lbs2017vuchihung-ops/Robot-aim-system-IOT/hardware/Main Aim to use/Main aim 3MG996R + 1SG90/Arduino based Robot Arm - 7322664/images/gear1.png

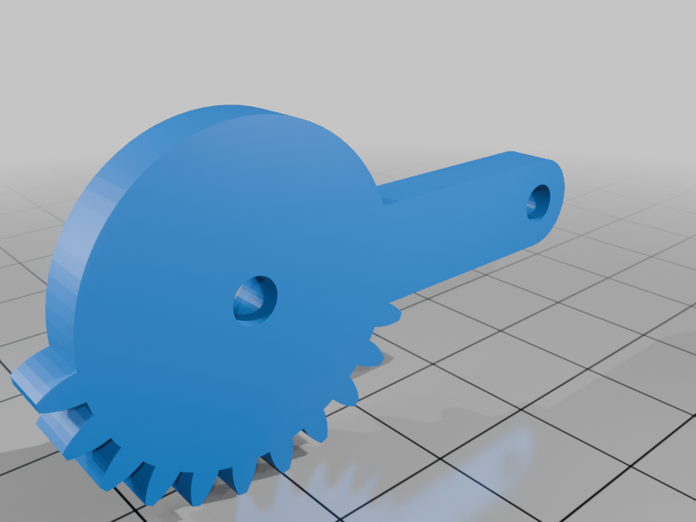
hardware/Main Aim to use/Main aim 3MG996R + 1SG90/Arduino based Robot Arm - 7322664/images/gear1.png
