lbs2017vuchihung-ops/Robot-aim-system-IOT/hardware/Reference Aims/EEZYbotARM MK2 - 1454048 - part 1 of 2/images/b436ef58e6b25d29e519d9658bfed57a.png

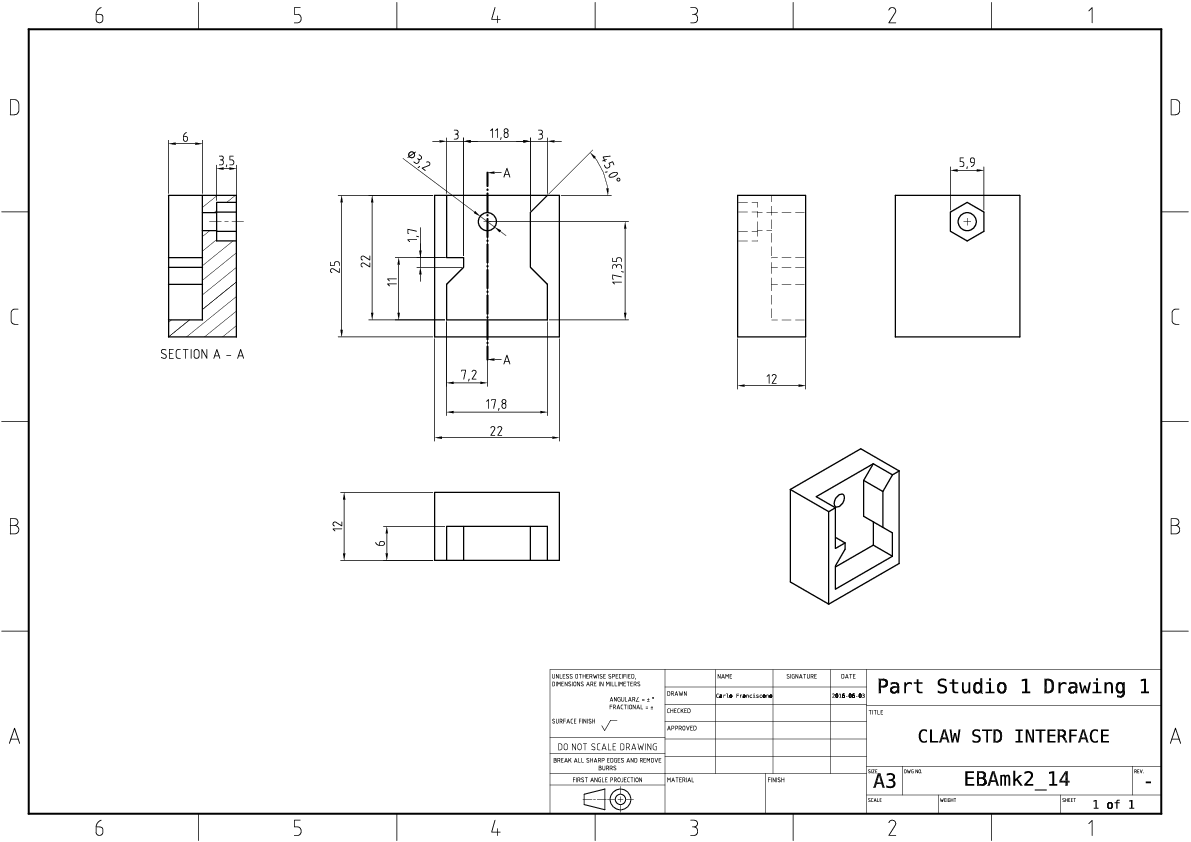
hardware/Reference Aims/EEZYbotARM MK2 - 1454048 - part 1 of 2/images/b436ef58e6b25d29e519d9658bfed57a.png
