lbs2017vuchihung-ops/Robot-aim-system-IOT/hardware/Reference Aims/Micro Servo SG90 - Dummy - 2933842/images/Micro_Servo_SG90.png

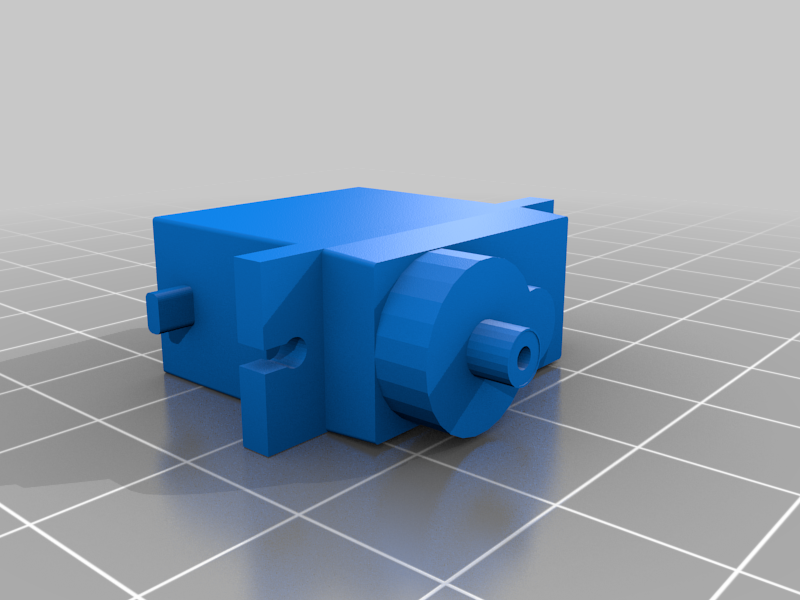
hardware/Reference Aims/Micro Servo SG90 - Dummy - 2933842/images/Micro_Servo_SG90.png
