lbs2017vuchihung-ops/Robot-aim-system-IOT/hardware/Reference Aims/Robotic arm 3 DOF V1 - 6986935/images/Starting_position_for_the_provided_code.jpg

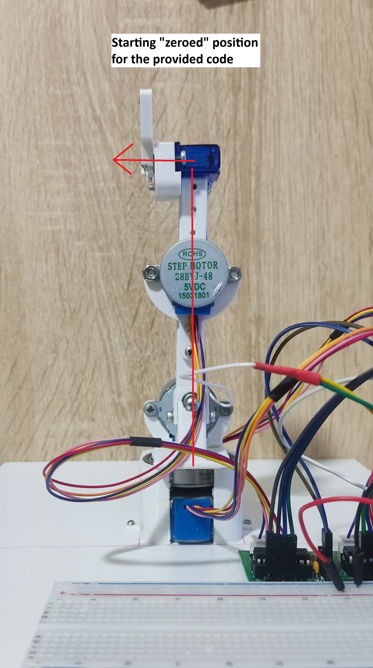
hardware/Reference Aims/Robotic arm 3 DOF V1 - 6986935/images/Starting_position_for_the_provided_code.jpg
