lbs2017vuchihung-ops/Robot-aim-system-IOT/hardware/Reference Aims/Robotic arm 3 DOF V1 - 6986935/images/View_1.jpg

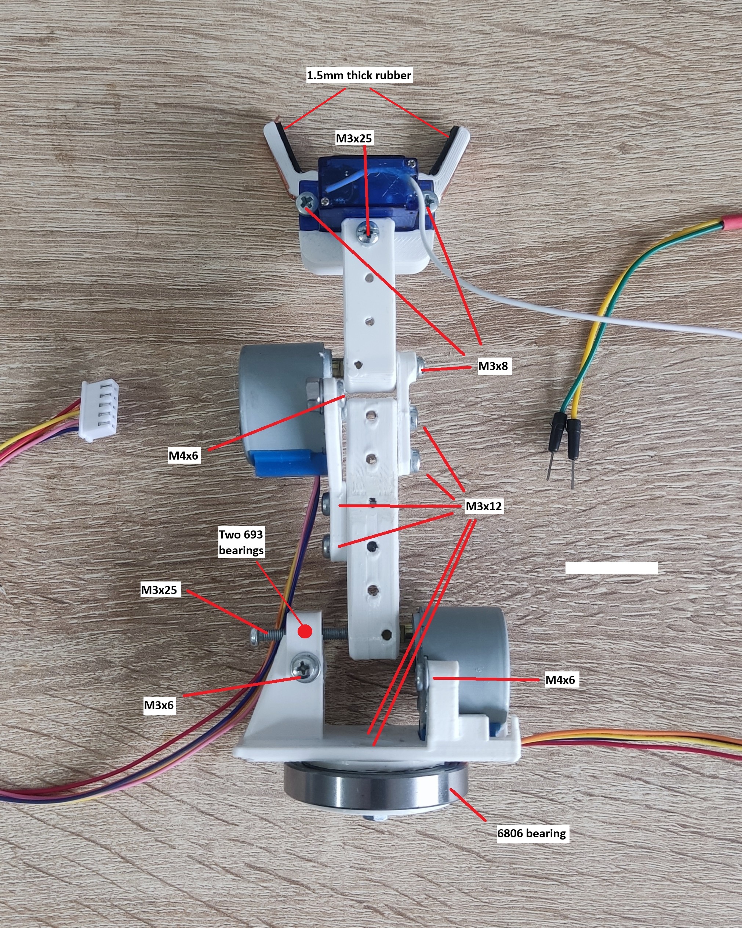
hardware/Reference Aims/Robotic arm 3 DOF V1 - 6986935/images/View_1.jpg
