lbs2017vuchihung-ops/Robot-aim-system-IOT/hardware/Reference Aims/Robotic Arm - 4 DOF - 3888877/images/photo5805476898975887829.jpg

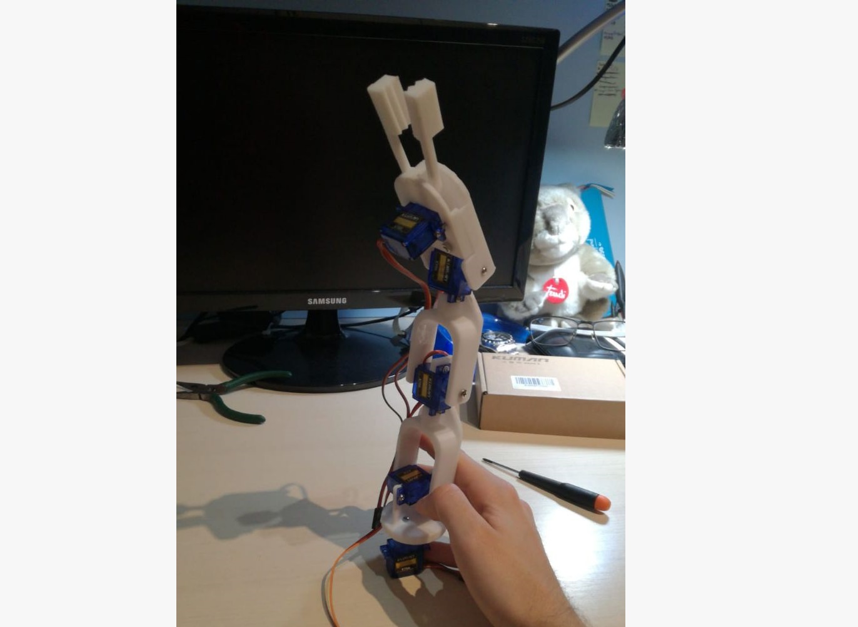
hardware/Reference Aims/Robotic Arm - 4 DOF - 3888877/images/photo5805476898975887829.jpg
