lbs2017vuchihung-ops/Robot-aim-system-IOT/hardware/Reference Aims/Robotic Arm - 4 DOF - 3888877/images/prt0003.png

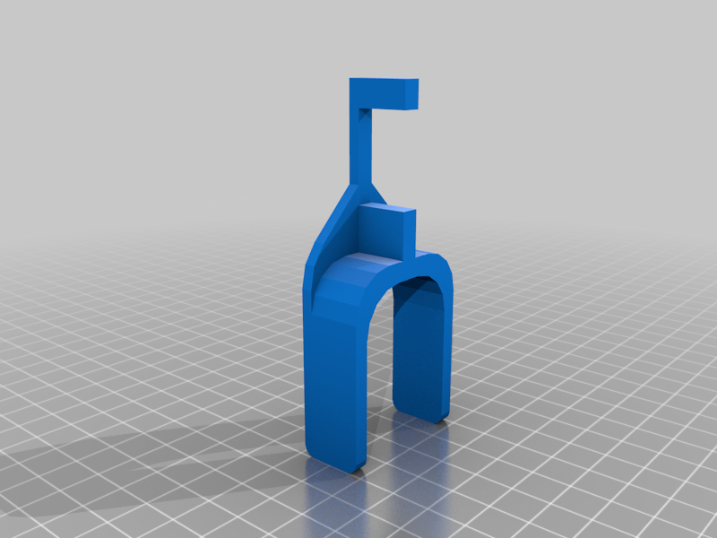
hardware/Reference Aims/Robotic Arm - 4 DOF - 3888877/images/prt0003.png
