lbs2017vuchihung-ops/Robot-aim-system-IOT/hardware/Reference Aims/Servo Arm_Horn for Tower Pro MG995_MG996R - 4719421/images/Servo_Arm.png

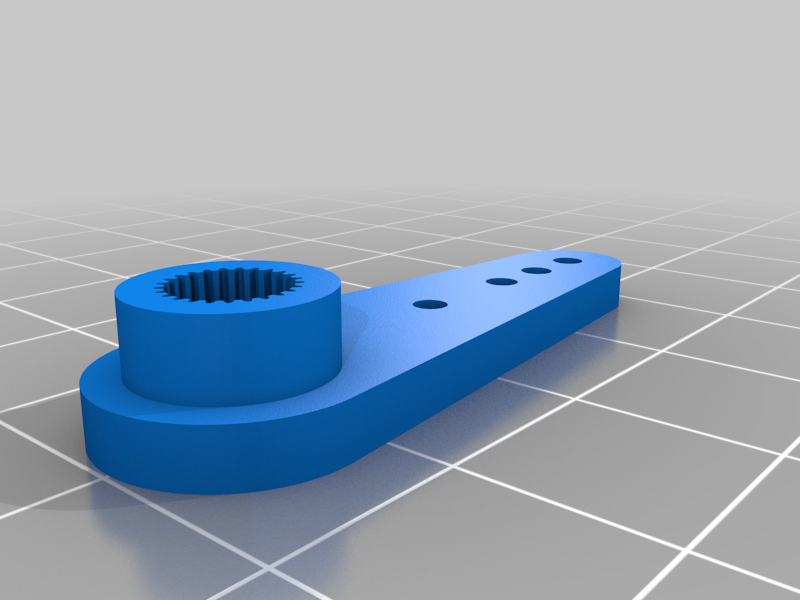
hardware/Reference Aims/Servo Arm_Horn for Tower Pro MG995_MG996R - 4719421/images/Servo_Arm.png
