lbs2017vuchihung-ops/Robot-aim-system-IOT/hardware/Reference Aims/Versatile Servo Bracket System - 5784/images/Servo_BracketOutsideLongV1.1.jpg

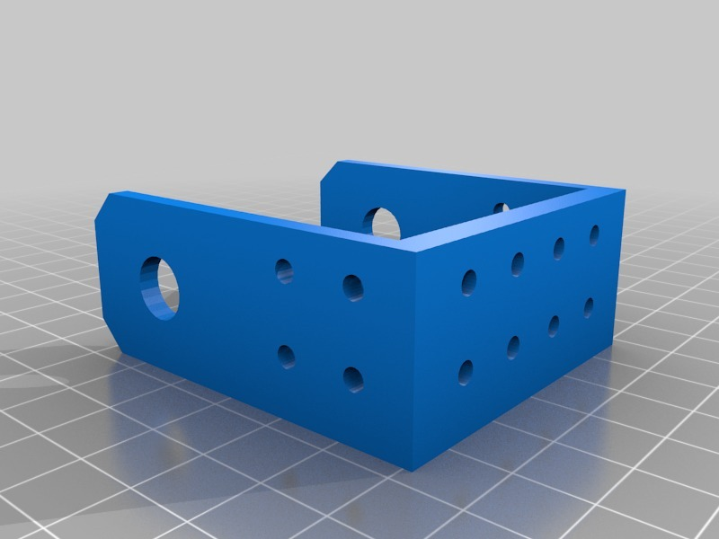
hardware/Reference Aims/Versatile Servo Bracket System - 5784/images/Servo_BracketOutsideLongV1.1.jpg
