lbs2017vuchihung-ops/Robot-aim-system-IOT/hardware/Reference Aims/Versatile Servo Bracket System - 5784/images/Servo_button.jpg

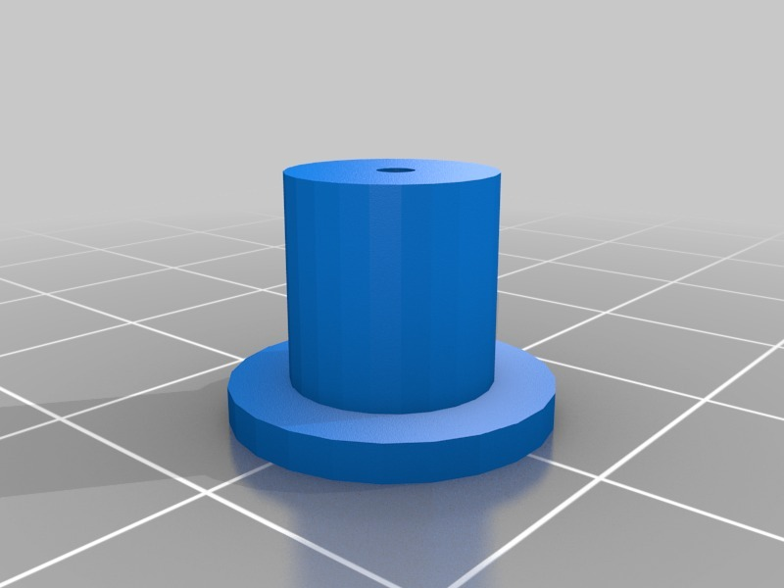
hardware/Reference Aims/Versatile Servo Bracket System - 5784/images/Servo_button.jpg
