lbs2017vuchihung-ops/Robot-aim-system-IOT/hardware/Reference Aims/Versatile Servo Bracket System - 5784/images/Servo_with_Button_display_large.jpg

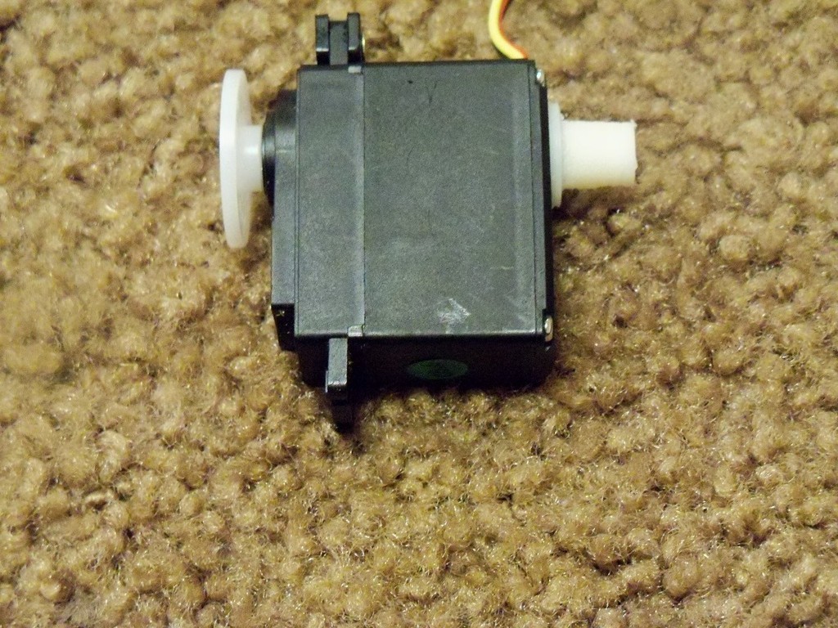
hardware/Reference Aims/Versatile Servo Bracket System - 5784/images/Servo_with_Button_display_large.jpg
