lbs2017vuchihung-ops/Robot-aim-system-IOT/web_app/assets/anh_adruino.png

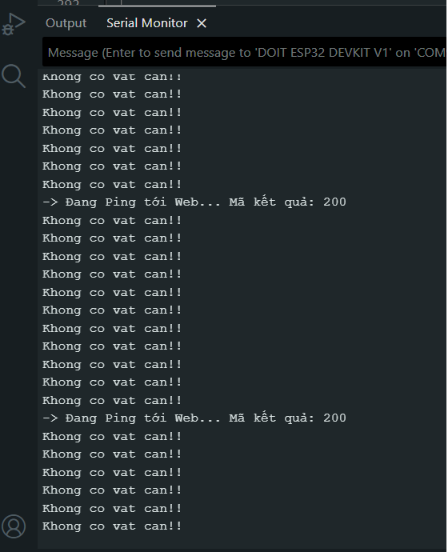
web_app/assets/anh_adruino.png
