lbs2017vuchihung-ops/Robot-aim-system-IOT/web_app/assets/anh_web.png

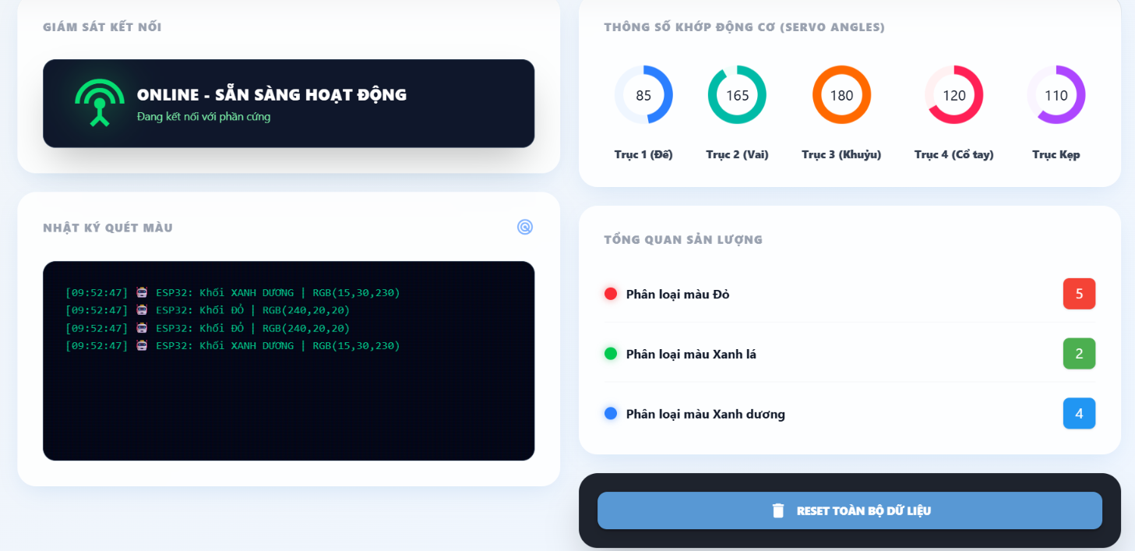
web_app/assets/anh_web.png
