lbs2017vuchihung-ops/Robot-aim-system-IOT/web_app/assets/RobotAimImg.jpg

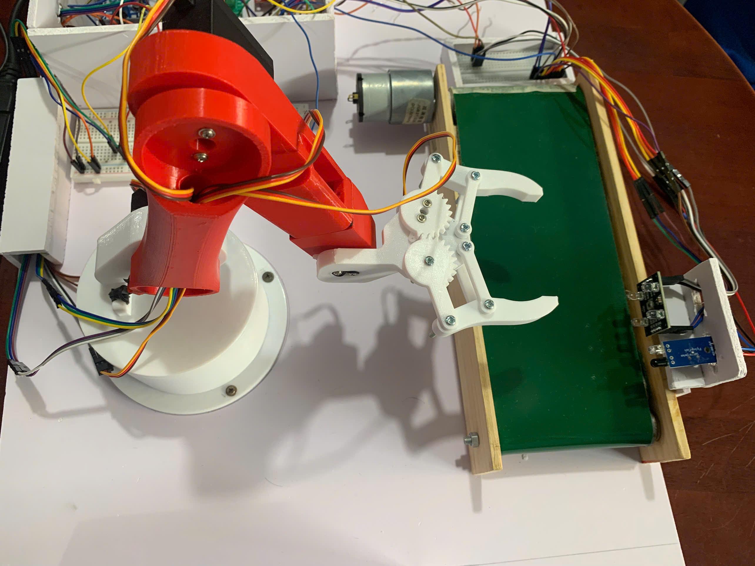
web_app/assets/RobotAimImg.jpg
