lbs2017vuchihung-ops/Robot-aim-system-IOT/hardware/Reference Aims/Versatile Servo Bracket System - 5784/images/Printed_Parts_display_large.jpg

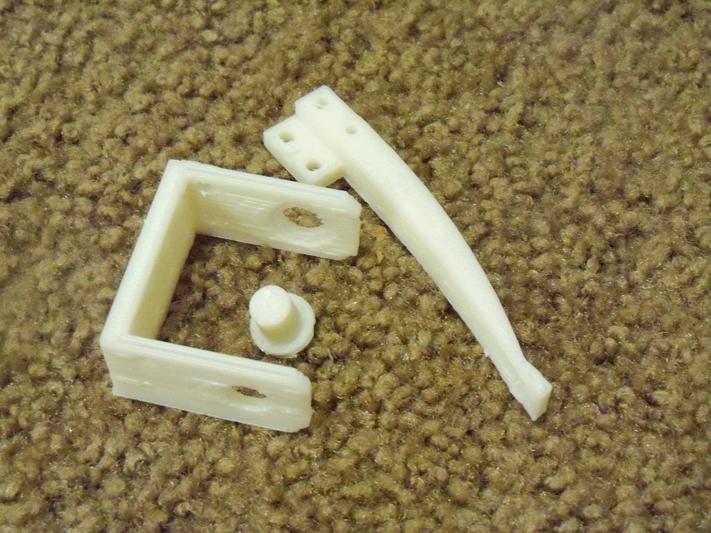
hardware/Reference Aims/Versatile Servo Bracket System - 5784/images/Printed_Parts_display_large.jpg
