lbs2017vuchihung-ops/Robot-aim-system-IOT/hardware/Reference Aims/Robotic Arm - 4 DOF - 3888877/files/prt0003.stl

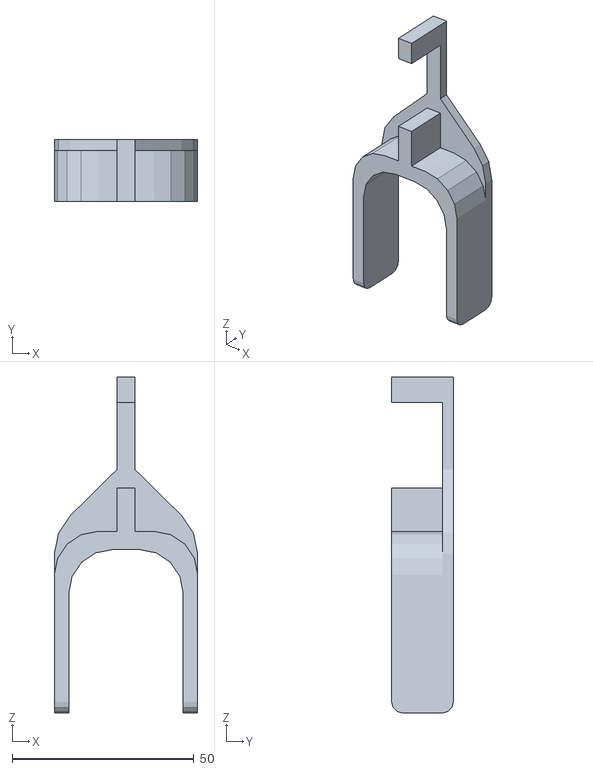
[picture p143: CAD file, 2026-08-05]
hardware/Reference Aims/Robotic Arm - 4 DOF - 3888877/files/prt0003.stl
39.5 x 17.0 x 92.5
