lbs2017vuchihung-ops/Robot-aim-system-IOT/hardware/Reference Aims/Robotic arm 3 DOF V1 - 6986935/files/28byj_mount.stl

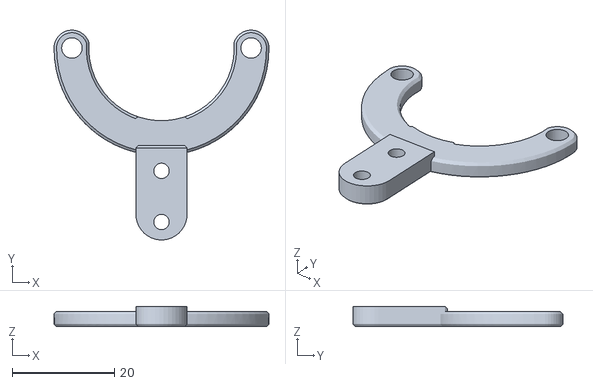
[picture p144: CAD file, 2026-08-05]
hardware/Reference Aims/Robotic arm 3 DOF V1 - 6986935/files/28byj_mount.stl
42.0 x 41.0 x 4.00
