lbs2017vuchihung-ops/Robot-aim-system-IOT/hardware/Reference Aims/Versatile Servo Bracket System - 5784/files/Servo_BracketInsideShortV1.1.stl

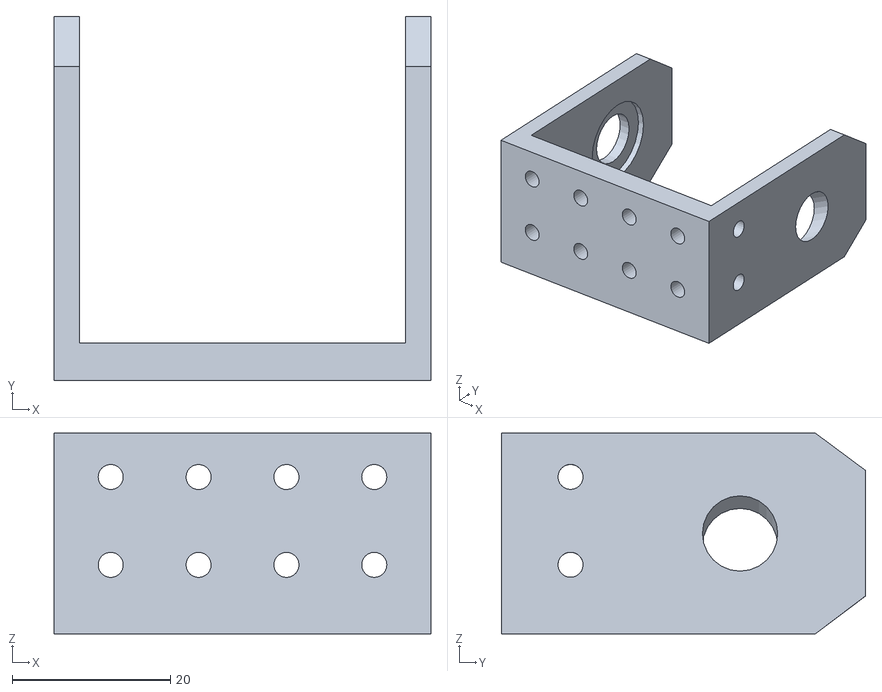
[picture p145: CAD file, 2026-08-05]
hardware/Reference Aims/Versatile Servo Bracket System - 5784/files/Servo_BracketInsideShortV1.1.stl
47.6 x 46.0 x 25.4
