lbs2017vuchihung-ops/Robot-aim-system-IOT/hardware/Main Aim to use/Main aim 3MG996R + 1SG90/Arduino based Robot Arm - 7322664/files/Arm_02_v3.STL

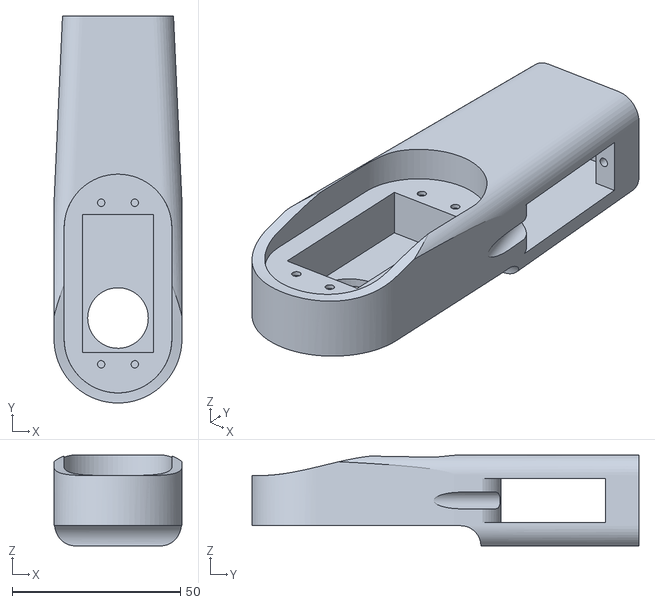
[picture p146: CAD file, 2026-08-05]
hardware/Main Aim to use/Main aim 3MG996R + 1SG90/Arduino based Robot Arm - 7322664/files/Arm_02_v3.STL
38.0 x 115.0 x 27.0
