lbs2017vuchihung-ops/Robot-aim-system-IOT/hardware/Reference Aims/EEZYbotARM MK2 - 1454048 - part 2 of 2/files/EBAmk2_003_varm.STL

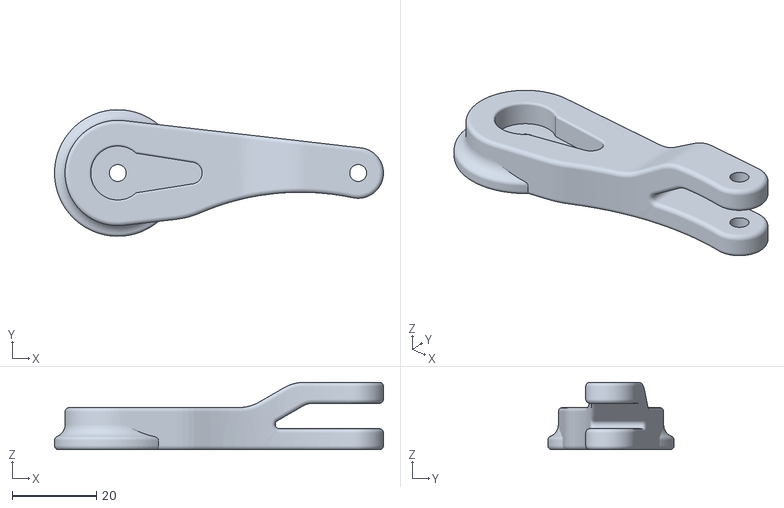
[picture p147: CAD file, 2026-08-05]
hardware/Reference Aims/EEZYbotARM MK2 - 1454048 - part 2 of 2/files/EBAmk2_003_varm.STL
78.0 x 30.0 x 16.0
