lbs2017vuchihung-ops/Robot-aim-system-IOT/hardware/Reference Aims/Robotic Arm - 4 DOF - 3888877/files/prt0001.stl

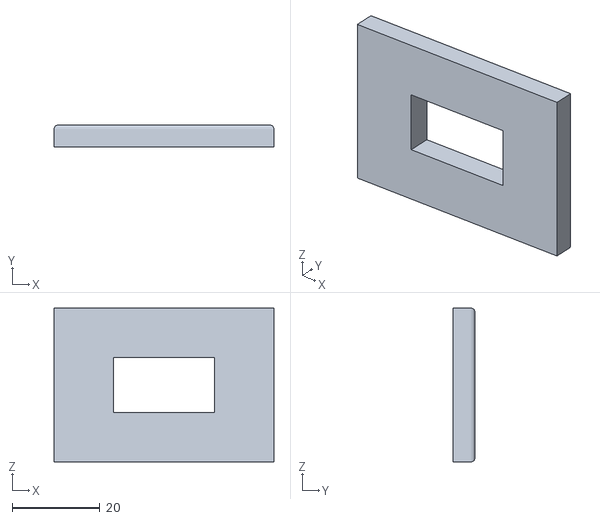
[picture p148: CAD file, 2026-08-05]
hardware/Reference Aims/Robotic Arm - 4 DOF - 3888877/files/prt0001.stl
50.0 x 5.00 x 35.0
