lbs2017vuchihung-ops/Robot-aim-system-IOT/hardware/Reference Aims/Robotic arm 3 DOF V1 - 6986935/files/Beam_support.stl

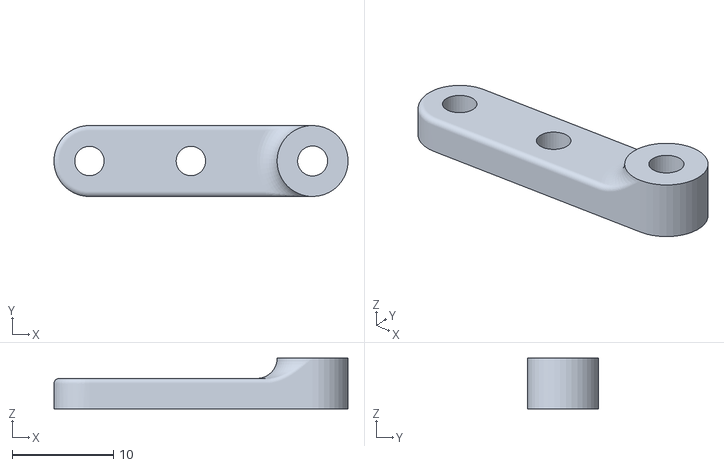
[picture p149: CAD file, 2026-08-05]
hardware/Reference Aims/Robotic arm 3 DOF V1 - 6986935/files/Beam_support.stl
29.0 x 7.00 x 5.00
