lbs2017vuchihung-ops/Robot-aim-system-IOT/hardware/Reference Aims/Versatile Servo Bracket System - 5784/files/Servo_BracketOutsideShortV1.1.stl

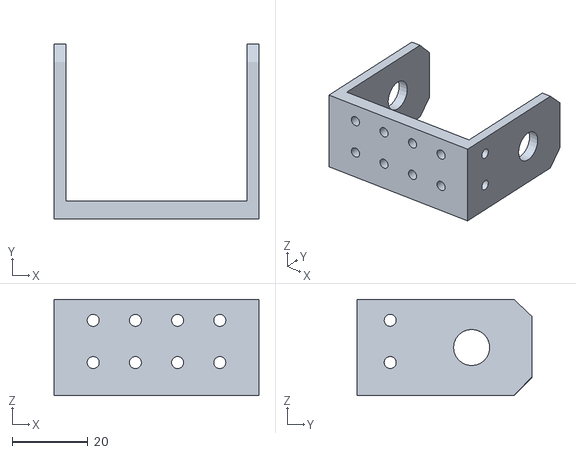
[picture p150: CAD file, 2026-08-05]
hardware/Reference Aims/Versatile Servo Bracket System - 5784/files/Servo_BracketOutsideShortV1.1.stl
54.0 x 46.1 x 25.4
