lbs2017vuchihung-ops/Robot-aim-system-IOT/hardware/Reference Aims/EEZYbotARM MK2 - 1454048 - part 2 of 2/files/EBAmk2_010_gearservo_22DENTI.STL

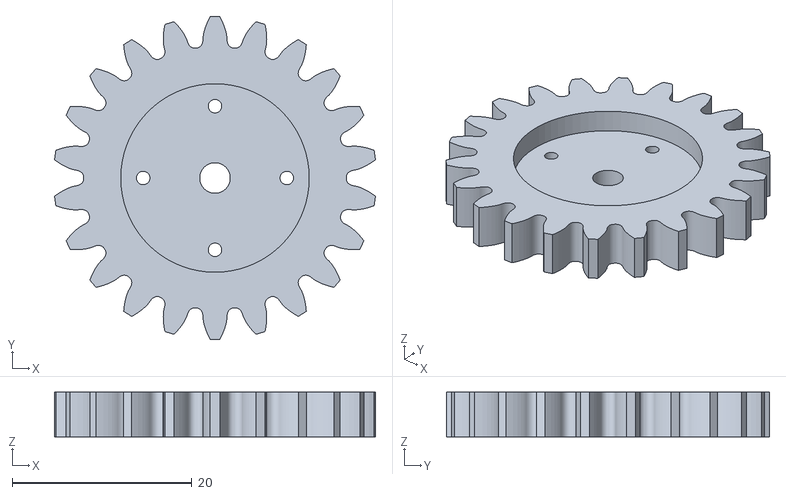
[picture p151: CAD file, 2026-08-05]
hardware/Reference Aims/EEZYbotARM MK2 - 1454048 - part 2 of 2/files/EBAmk2_010_gearservo_22DENTI.STL
35.8 x 36.0 x 5.00
