lbs2017vuchihung-ops/Robot-aim-system-IOT/hardware/Reference Aims/Robotic Arm - 4 DOF - 3888877/files/prt0011.stl

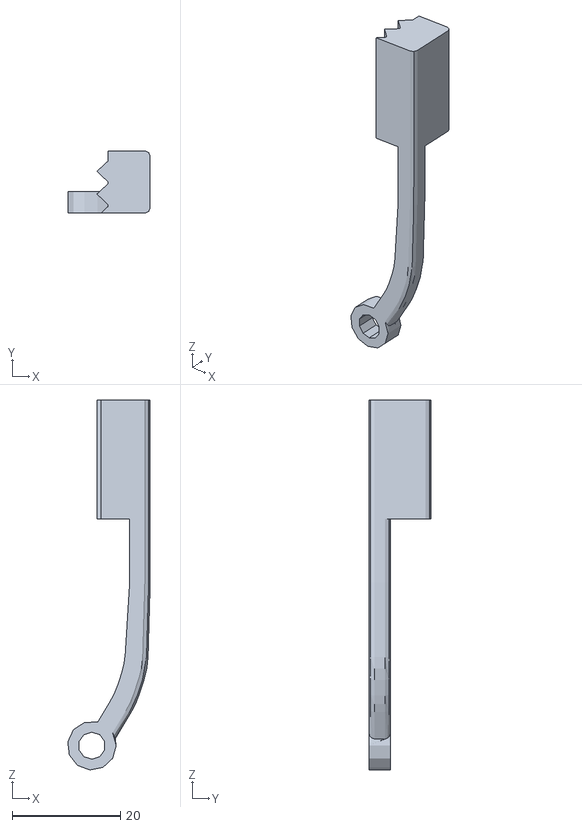
[picture p152: CAD file, 2026-08-05]
hardware/Reference Aims/Robotic Arm - 4 DOF - 3888877/files/prt0011.stl
15.2 x 11.5 x 68.3
