lbs2017vuchihung-ops/Robot-aim-system-IOT/hardware/Reference Aims/Robotic arm 3 DOF V1 - 6986935/files/EE_SG90_mount.stl

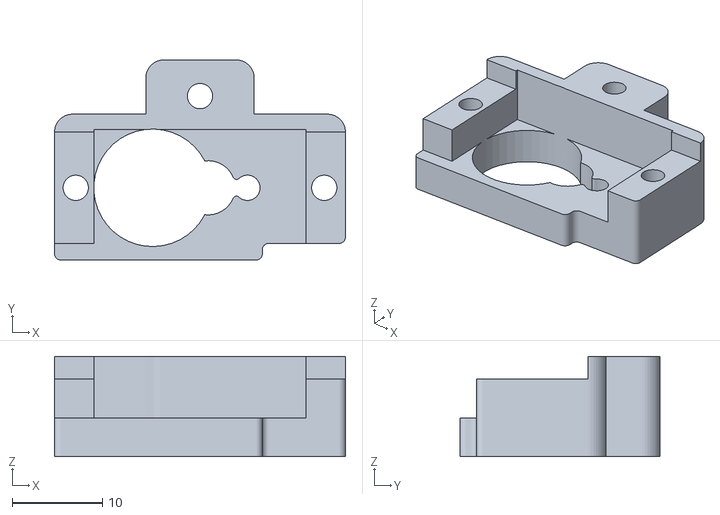
[picture p153: CAD file, 2026-08-05]
hardware/Reference Aims/Robotic arm 3 DOF V1 - 6986935/files/EE_SG90_mount.stl
32.2 x 22.1 x 11.1
