lbs2017vuchihung-ops/Robot-aim-system-IOT/hardware/Reference Aims/Versatile Servo Bracket System - 5784/files/Servo_Leg.stl

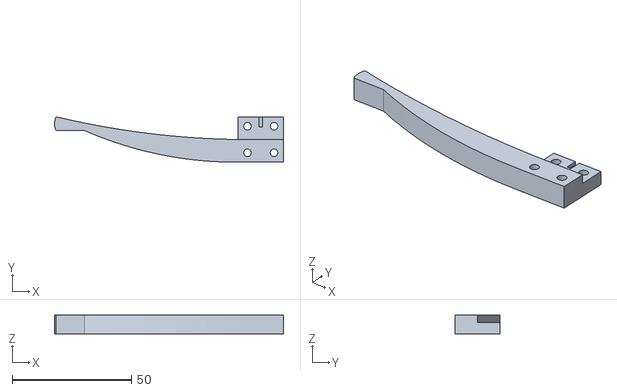
[picture p154: CAD file, 2026-08-05]
hardware/Reference Aims/Versatile Servo Bracket System - 5784/files/Servo_Leg.stl
95.9 x 19.1 x 7.94
