lbs2017vuchihung-ops/Robot-aim-system-IOT/hardware/Main Aim to use/Main aim 3MG996R + 1SG90/Arduino based Robot Arm - 7322664/files/Gripper_1.STL

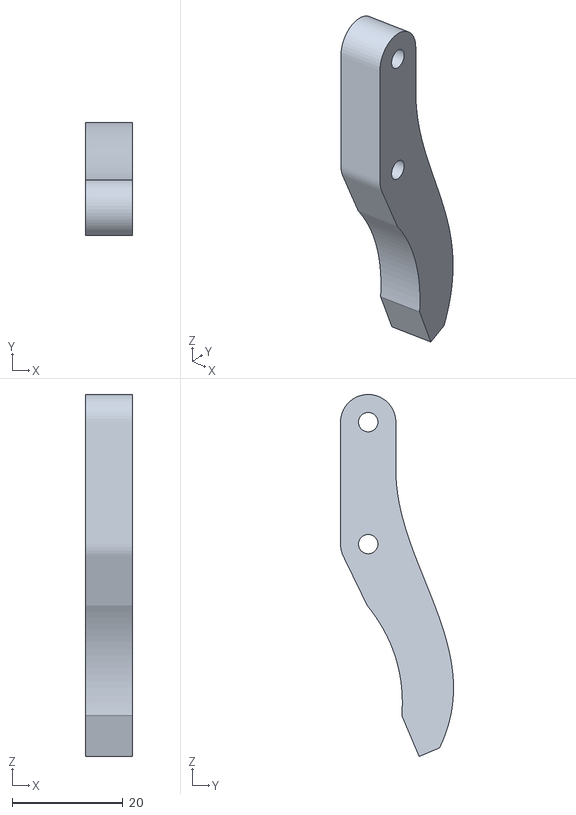
[picture p155: CAD file, 2026-08-05]
hardware/Main Aim to use/Main aim 3MG996R + 1SG90/Arduino based Robot Arm - 7322664/files/Gripper_1.STL
8.50 x 20.4 x 65.3
