lbs2017vuchihung-ops/Robot-aim-system-IOT/hardware/Reference Aims/EEZYbotARM MK2 - 1454048 - part 2 of 2/files/EBAmk2_006_horarm__.STL

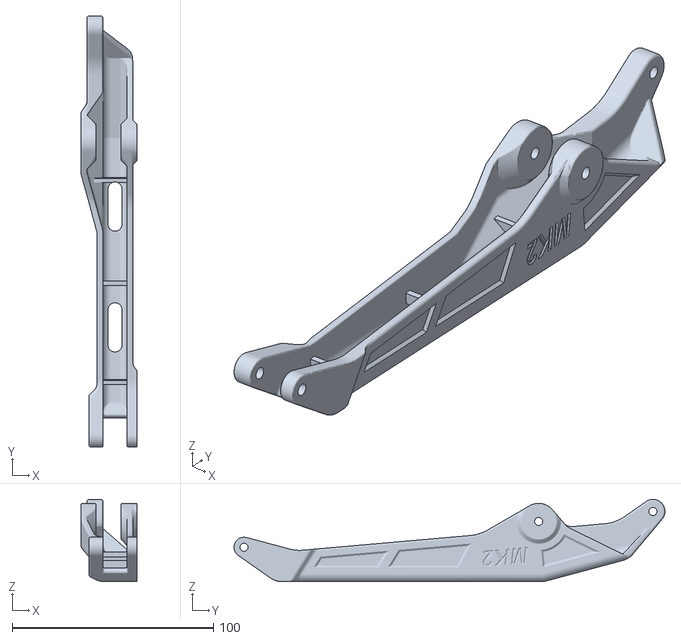
[picture p156: CAD file, 2026-08-05]
hardware/Reference Aims/EEZYbotARM MK2 - 1454048 - part 2 of 2/files/EBAmk2_006_horarm__.STL
28.0 x 214.2 x 40.9
