lbs2017vuchihung-ops/Robot-aim-system-IOT/hardware/Reference Aims/Robotic Arm - 4 DOF - 3888877/files/prt0002.stl

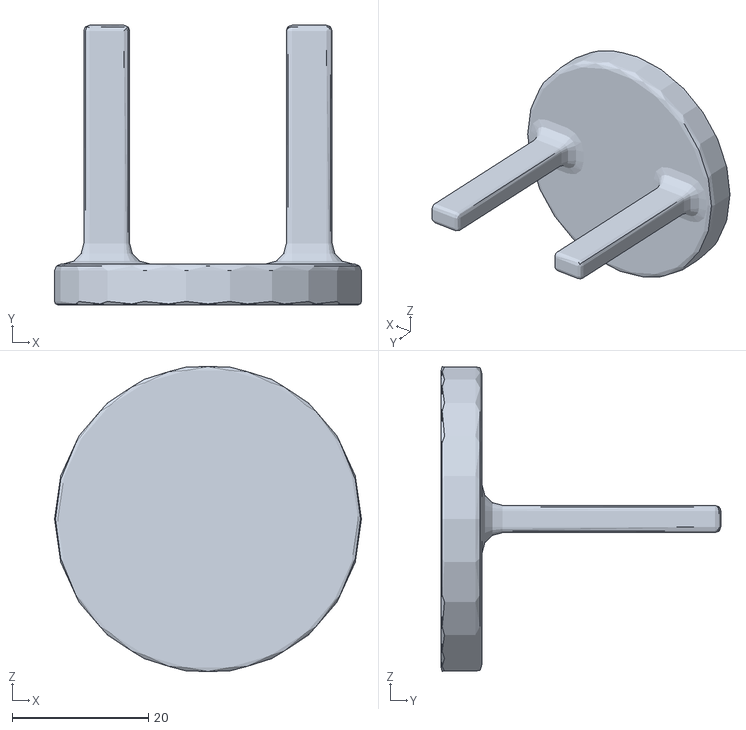
[picture p157: CAD file, 2026-08-05]
hardware/Reference Aims/Robotic Arm - 4 DOF - 3888877/files/prt0002.stl
45.0 x 41.0 x 44.7
