lbs2017vuchihung-ops/Robot-aim-system-IOT/hardware/Reference Aims/Robotic arm 3 DOF V1 - 6986935/files/BASE.stl

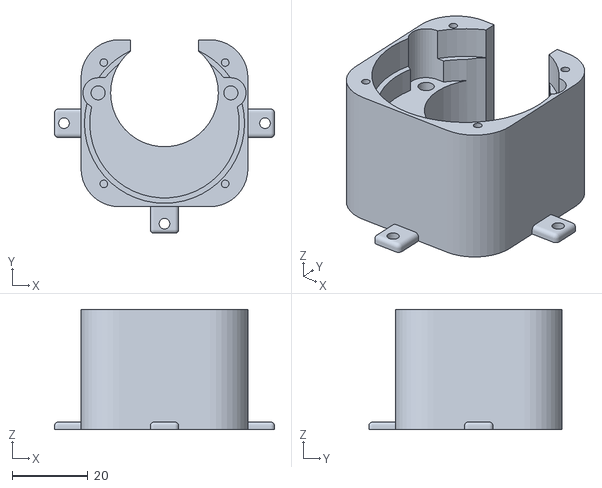
[picture p158: CAD file, 2026-08-05]
hardware/Reference Aims/Robotic arm 3 DOF V1 - 6986935/files/BASE.stl
58.0 x 51.0 x 31.7
