lbs2017vuchihung-ops/Robot-aim-system-IOT/hardware/Reference Aims/Versatile Servo Bracket System - 5784/files/Servo_ConnectorOutside3DOF.stl

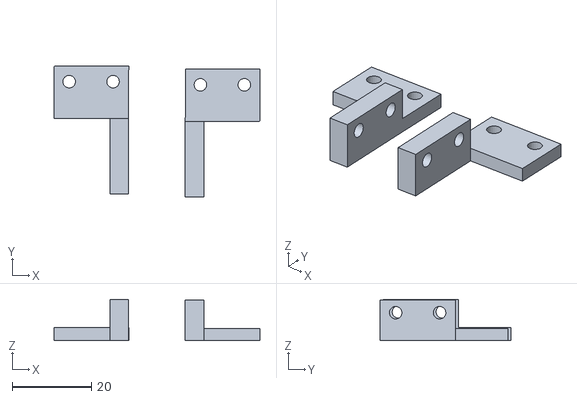
[picture p159: CAD file, 2026-08-05]
hardware/Reference Aims/Versatile Servo Bracket System - 5784/files/Servo_ConnectorOutside3DOF.stl
52.1 x 33.2 x 10.5
