lbs2017vuchihung-ops/Robot-aim-system-IOT/hardware/Main Aim to use/Main aim 3MG996R + 1SG90/Arduino based Robot Arm - 7322664/files/Base.STL

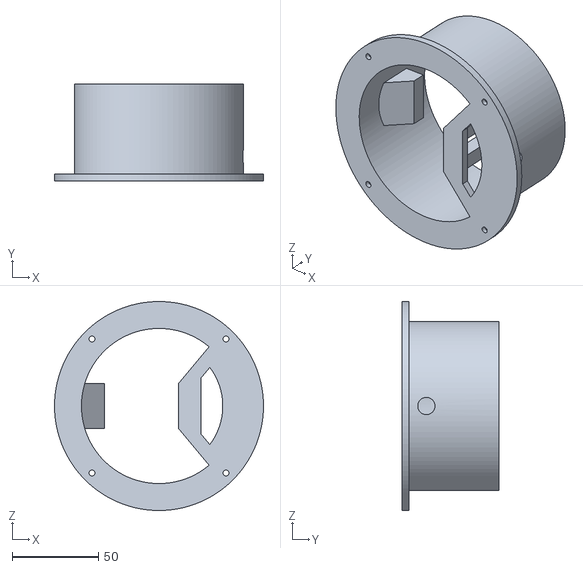
[picture p160: CAD file, 2026-08-05]
hardware/Main Aim to use/Main aim 3MG996R + 1SG90/Arduino based Robot Arm - 7322664/files/Base.STL
121.2 x 56.0 x 121.2
