lbs2017vuchihung-ops/Robot-aim-system-IOT/hardware/Reference Aims/EEZYbotARM MK2 - 1454048 - part 2 of 2/files/EBAmk2_013_lower_base.STL

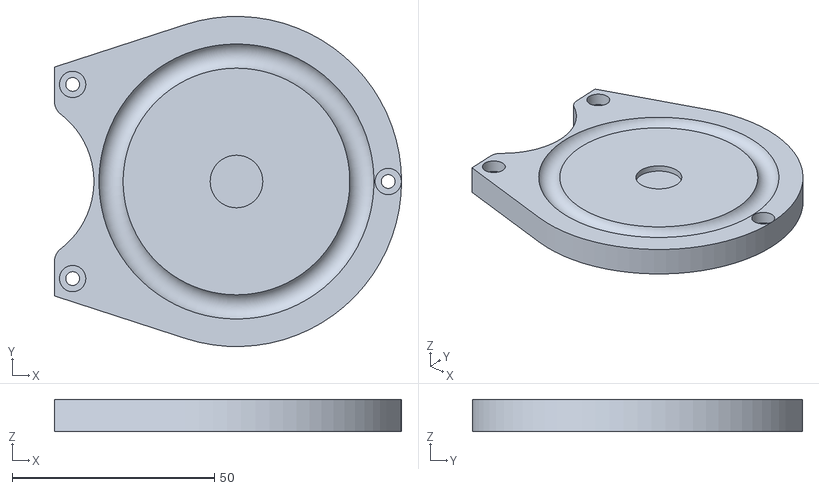
[picture p161: CAD file, 2026-08-05]
hardware/Reference Aims/EEZYbotARM MK2 - 1454048 - part 2 of 2/files/EBAmk2_013_lower_base.STL
85.8 x 81.6 x 8.00
