lbs2017vuchihung-ops/Robot-aim-system-IOT/hardware/Reference Aims/Robotic Arm - 4 DOF - 3888877/files/prt0005.stl

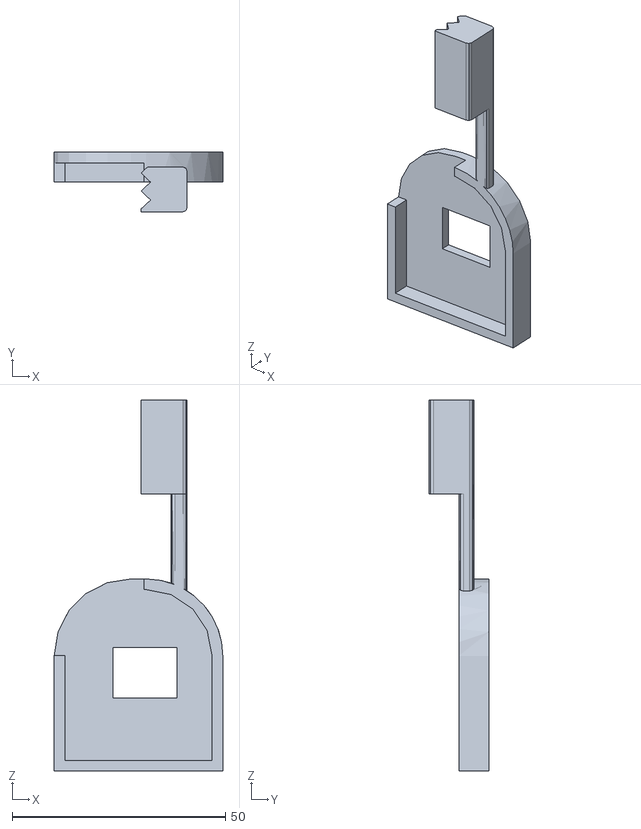
[picture p162: CAD file, 2026-08-05]
hardware/Reference Aims/Robotic Arm - 4 DOF - 3888877/files/prt0005.stl
39.5 x 14.0 x 86.9
