lbs2017vuchihung-ops/Robot-aim-system-IOT/hardware/Reference Aims/Robotic arm 3 DOF V1 - 6986935/files/Tolerance_test_print.stl

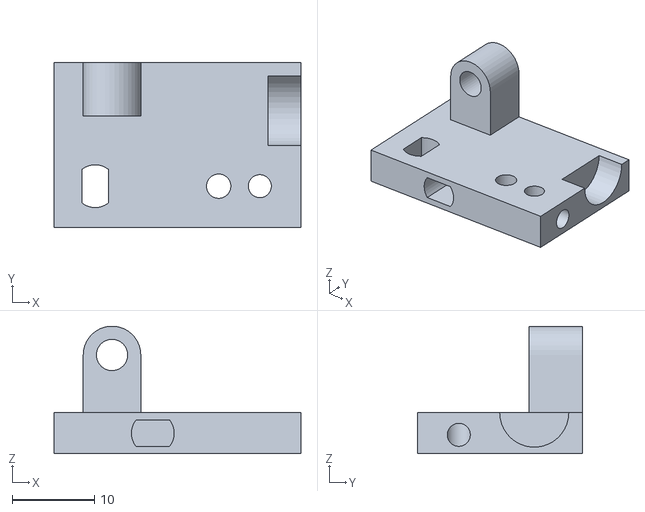
[picture p163: CAD file, 2026-08-05]
hardware/Reference Aims/Robotic arm 3 DOF V1 - 6986935/files/Tolerance_test_print.stl
30.0 x 20.0 x 15.5
