lbs2017vuchihung-ops/Robot-aim-system-IOT/hardware/Reference Aims/Versatile Servo Bracket System - 5784/files/Servo_BracketOutsideLongV1.1.stl

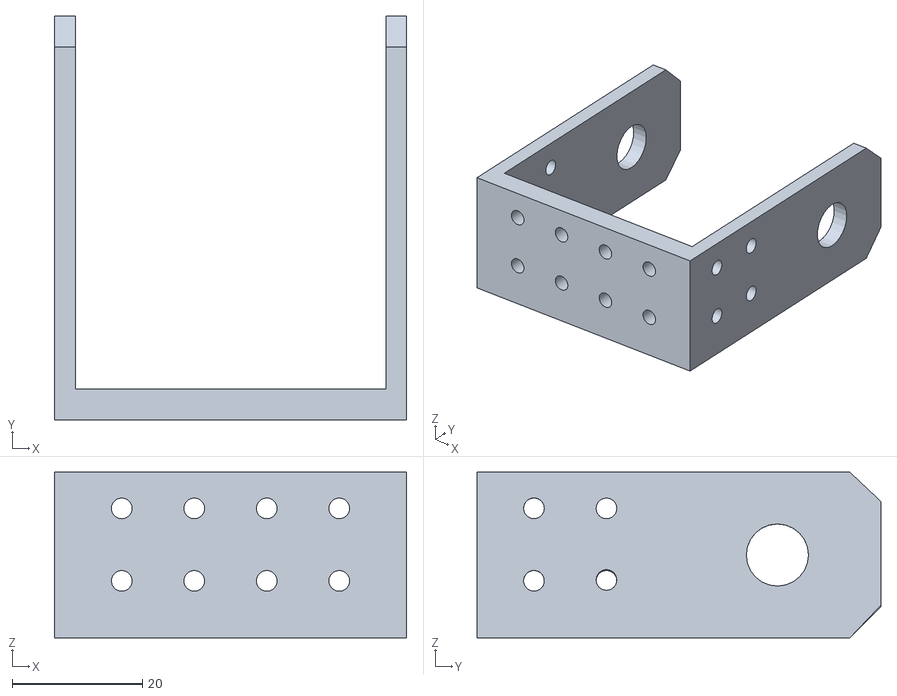
[picture p164: CAD file, 2026-08-05]
hardware/Reference Aims/Versatile Servo Bracket System - 5784/files/Servo_BracketOutsideLongV1.1.stl
54.0 x 61.9 x 25.4
