lbs2017vuchihung-ops/Robot-aim-system-IOT/hardware/Main Aim to use/Main aim 3MG996R + 1SG90/Arduino based Robot Arm - 7322664/files/Gripper_base.STL

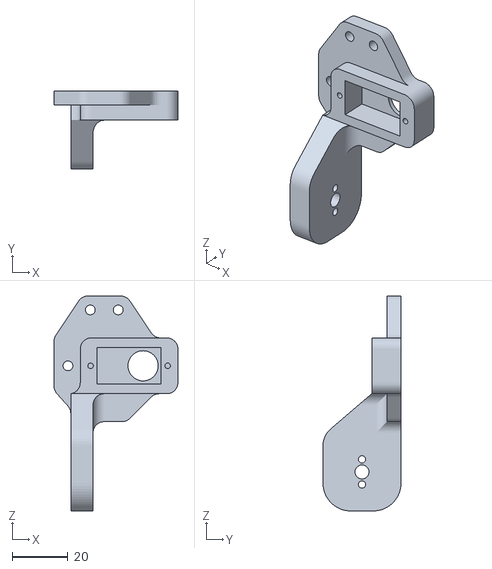
[picture p165: CAD file, 2026-08-05]
hardware/Main Aim to use/Main aim 3MG996R + 1SG90/Arduino based Robot Arm - 7322664/files/Gripper_base.STL
44.4 x 28.0 x 77.0
