lbs2017vuchihung-ops/Robot-aim-system-IOT/hardware/Reference Aims/EEZYbotARM MK2 - 1454048 - part 2 of 2/files/EBAmk2_005_link135angled.STL

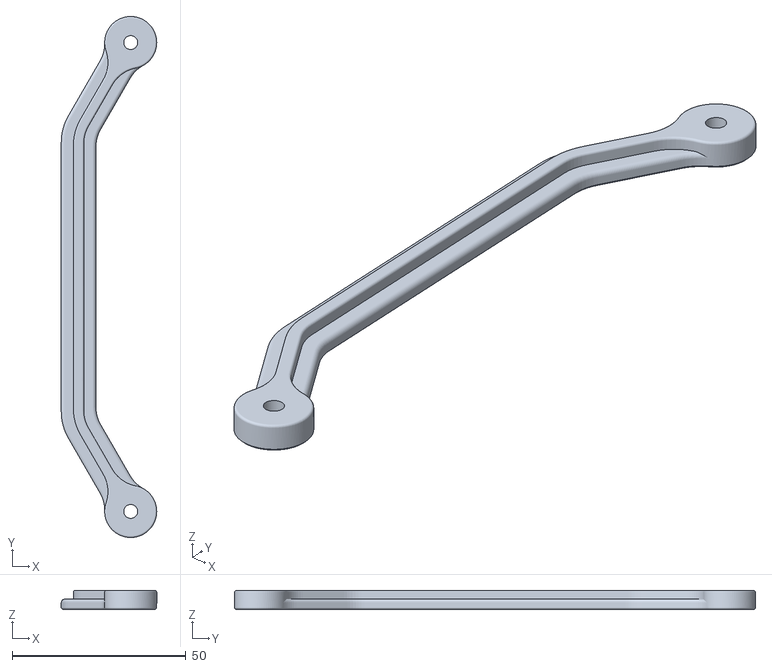
[picture p166: CAD file, 2026-08-05]
hardware/Reference Aims/EEZYbotARM MK2 - 1454048 - part 2 of 2/files/EBAmk2_005_link135angled.STL
27.5 x 150.0 x 5.50
