lbs2017vuchihung-ops/Robot-aim-system-IOT/hardware/Reference Aims/Versatile Servo Bracket System - 5784/files/Servo_ConnectorInside3DOF.stl

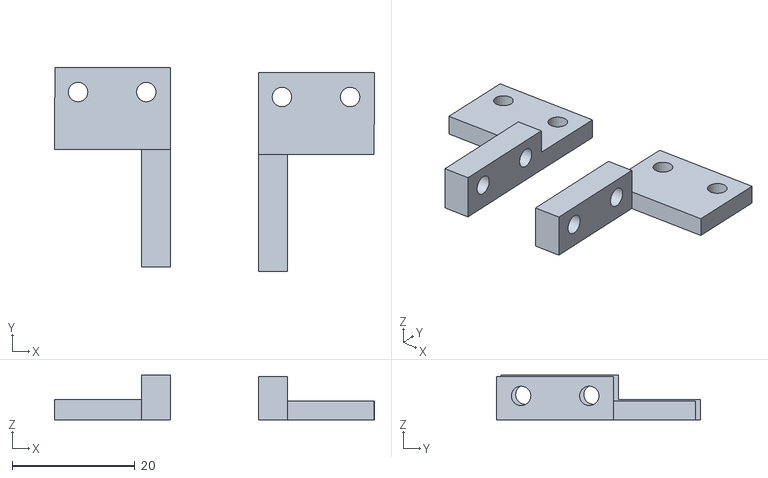
[picture p168: CAD file, 2026-08-05]
hardware/Reference Aims/Versatile Servo Bracket System - 5784/files/Servo_ConnectorInside3DOF.stl
52.1 x 33.2 x 7.29
