lbs2017vuchihung-ops/Robot-aim-system-IOT/hardware/Main Aim to use/Main aim 3MG996R + 1SG90/Arduino based Robot Arm - 7322664/files/Arm_03.STL

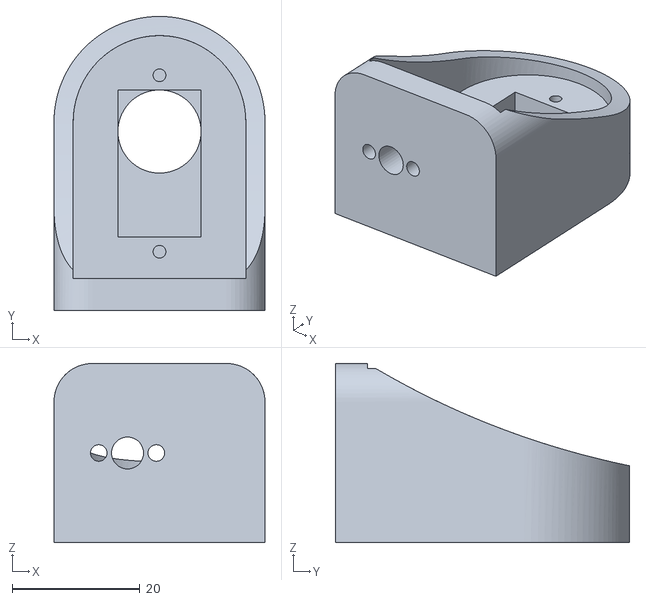
[picture p169: CAD file, 2026-08-05]
hardware/Main Aim to use/Main aim 3MG996R + 1SG90/Arduino based Robot Arm - 7322664/files/Arm_03.STL
33.0 x 46.0 x 28.0
