lbs2017vuchihung-ops/Robot-aim-system-IOT/hardware/Reference Aims/Robotic arm 3 DOF V1 - 6986935/files/SG90_EE_L_finger_.stl

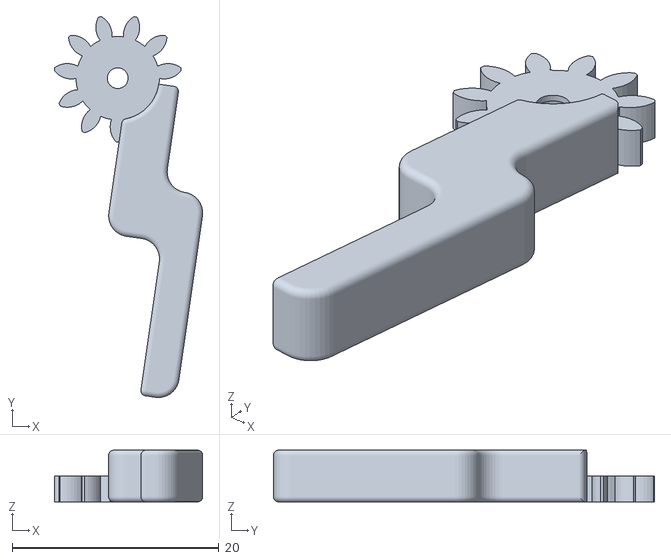
[picture p178: CAD file, 2026-08-05]
hardware/Reference Aims/Robotic arm 3 DOF V1 - 6986935/files/SG90_EE_L_finger_.stl
14.3 x 36.8 x 5.00
