lbs2017vuchihung-ops/Robot-aim-system-IOT/hardware/Reference Aims/Robotic arm 3 DOF V1 - 6986935/files/SG90_EE_R_finger_.stl

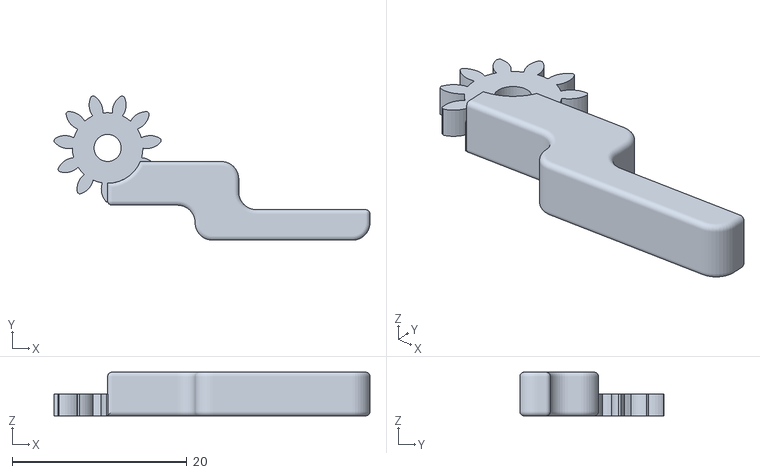
[picture p180: CAD file, 2026-08-05]
hardware/Reference Aims/Robotic arm 3 DOF V1 - 6986935/files/SG90_EE_R_finger_.stl
36.1 x 16.5 x 5.00
