lbs2017vuchihung-ops/Robot-aim-system-IOT/hardware/Reference Aims/Robotic arm 3 DOF V1 - 6986935/files/Beam_5_with_counterweight.stl

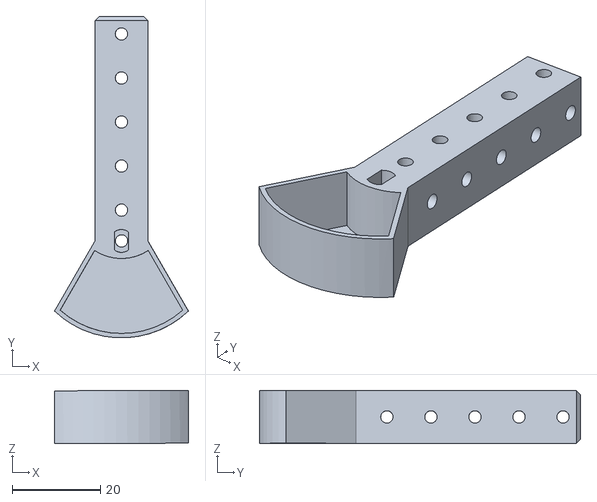
[picture p182: CAD file, 2026-08-05]
hardware/Reference Aims/Robotic arm 3 DOF V1 - 6986935/files/Beam_5_with_counterweight.stl
30.4 x 73.0 x 12.1
