lbs2017vuchihung-ops/Robot-aim-system-IOT/hardware/Reference Aims/Robotic arm 3 DOF V1 - 6986935/images/Tolerance_test_print.png

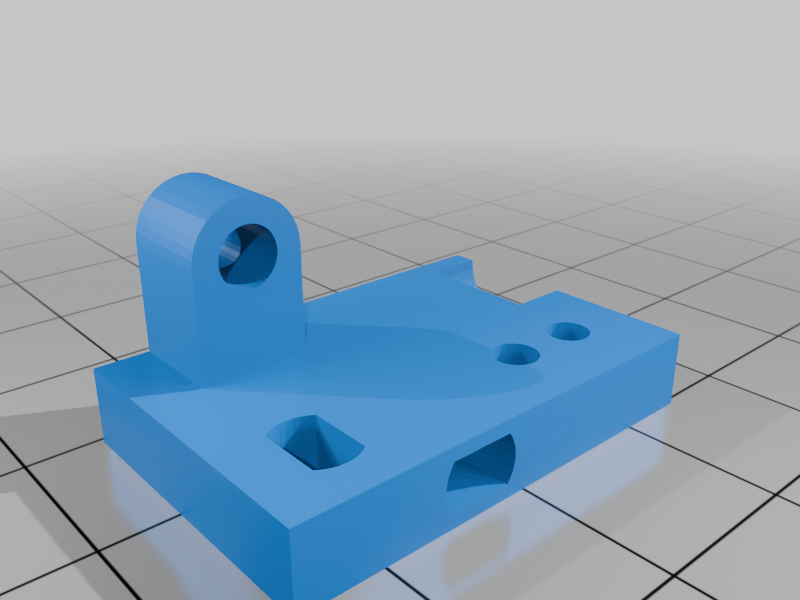
hardware/Reference Aims/Robotic arm 3 DOF V1 - 6986935/images/Tolerance_test_print.png
